schlae/goodgreat-ds3/GreengateDS3.kicad_sch

## KiCad design GreengateDS3.kicad_sch (2024-04-06)

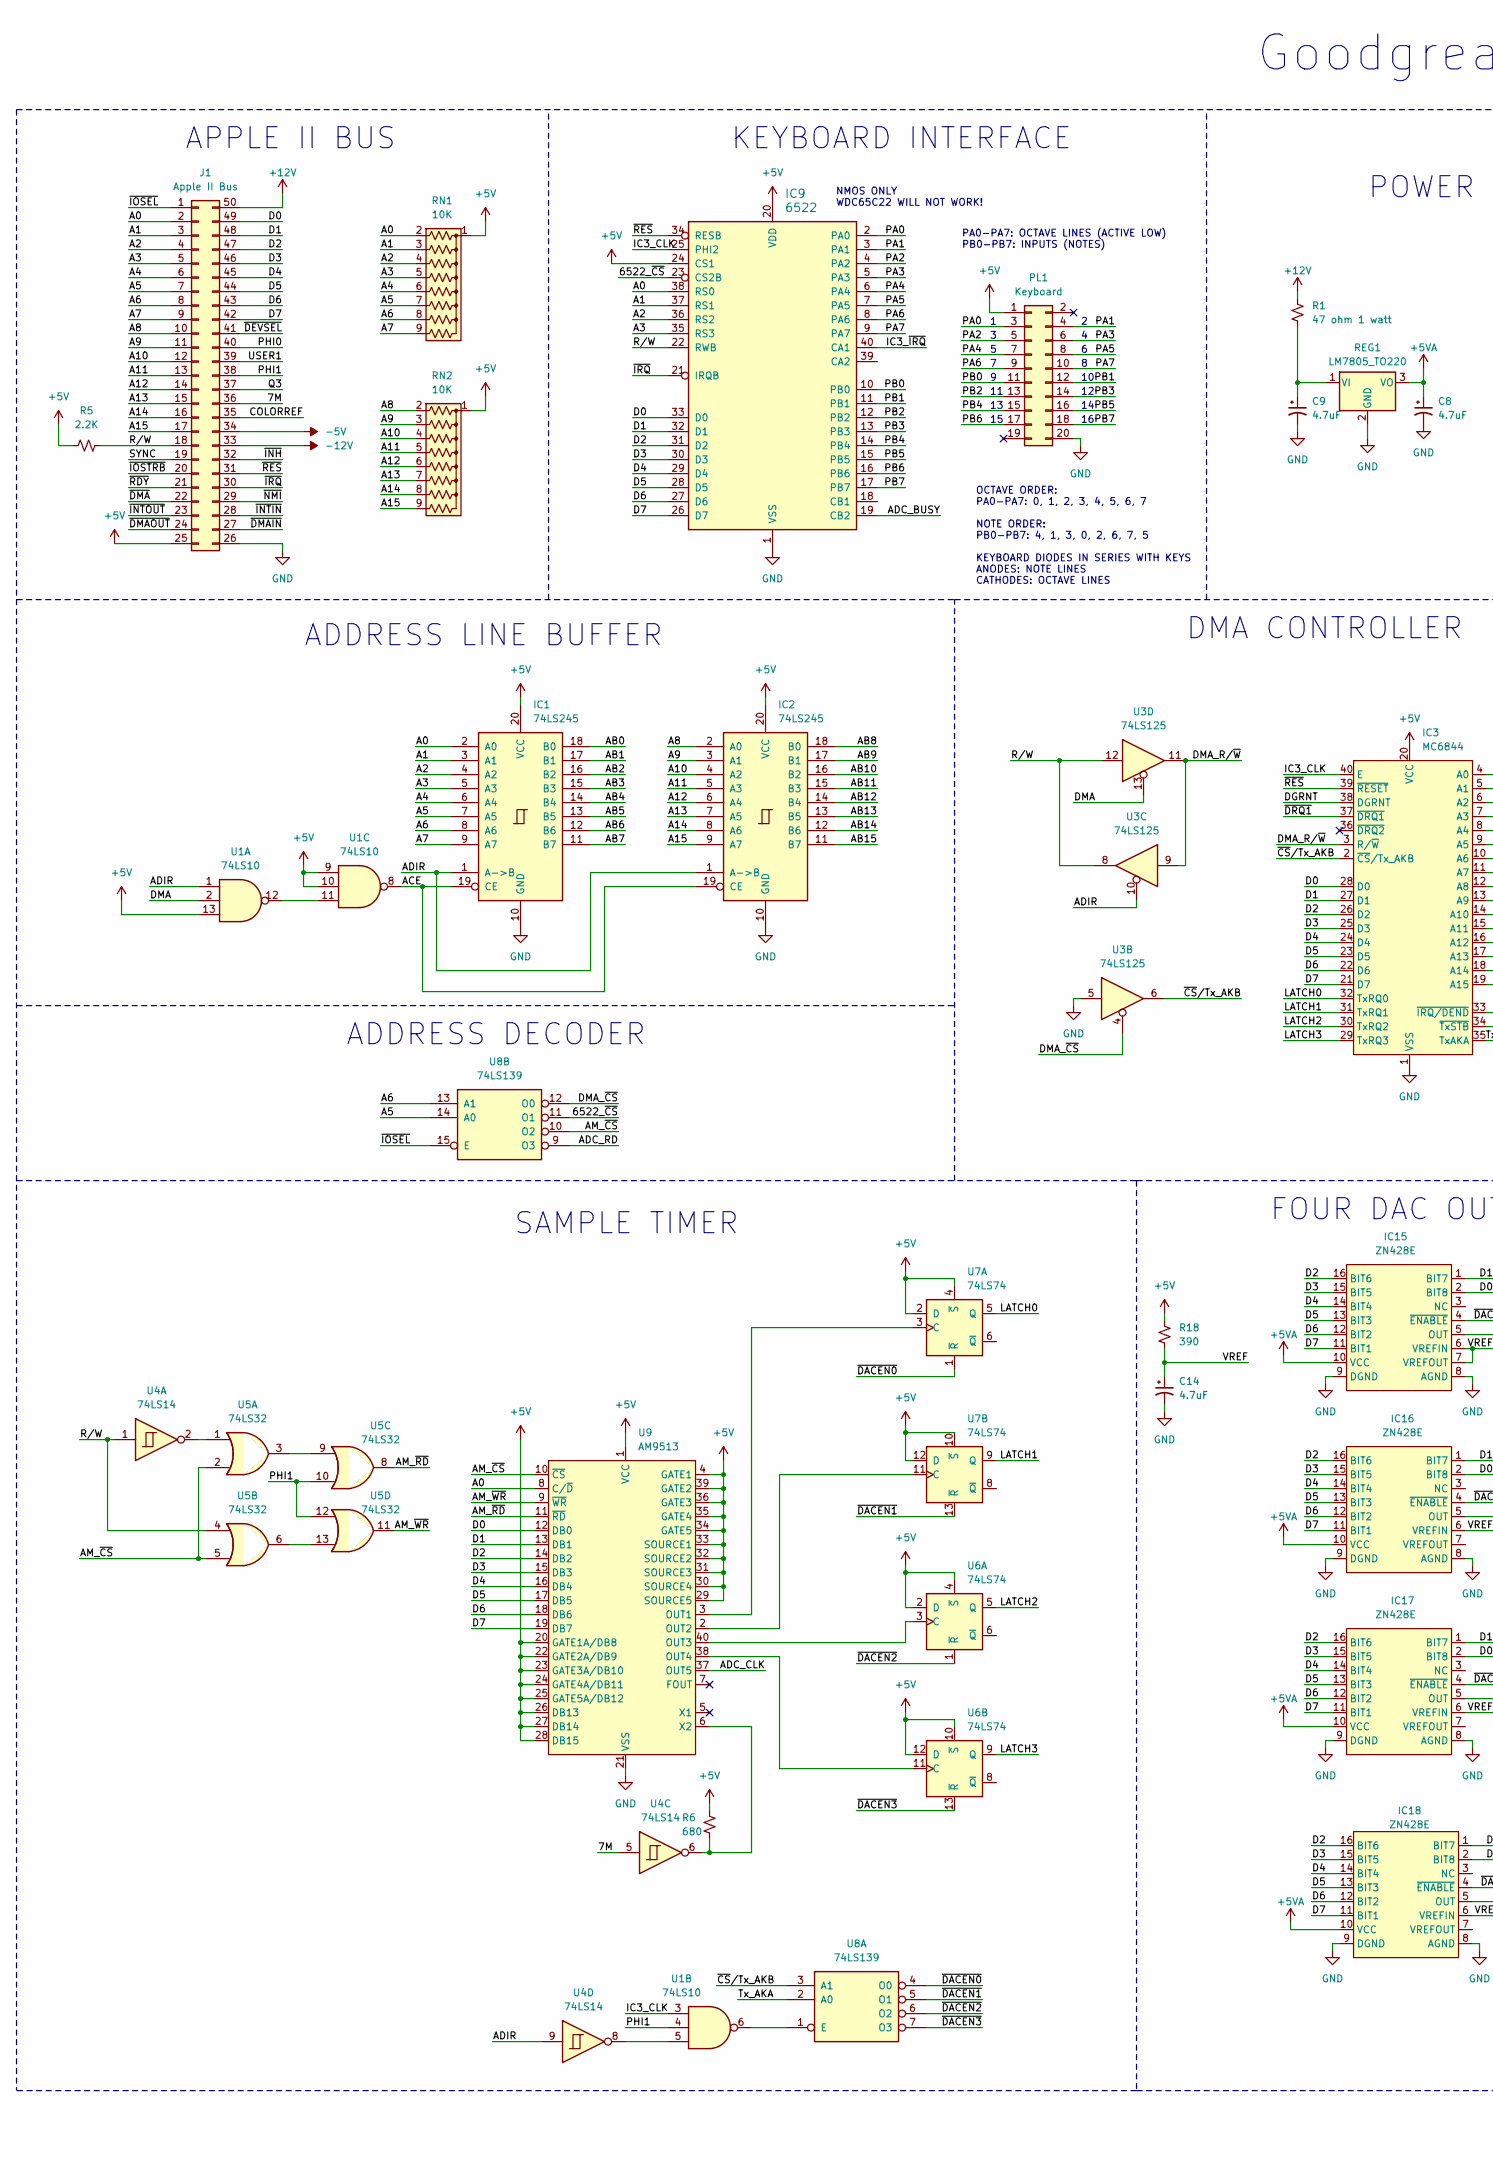
[picture p4: schematic GreengateDS3.kicad_sch, part in row 1, column 1]

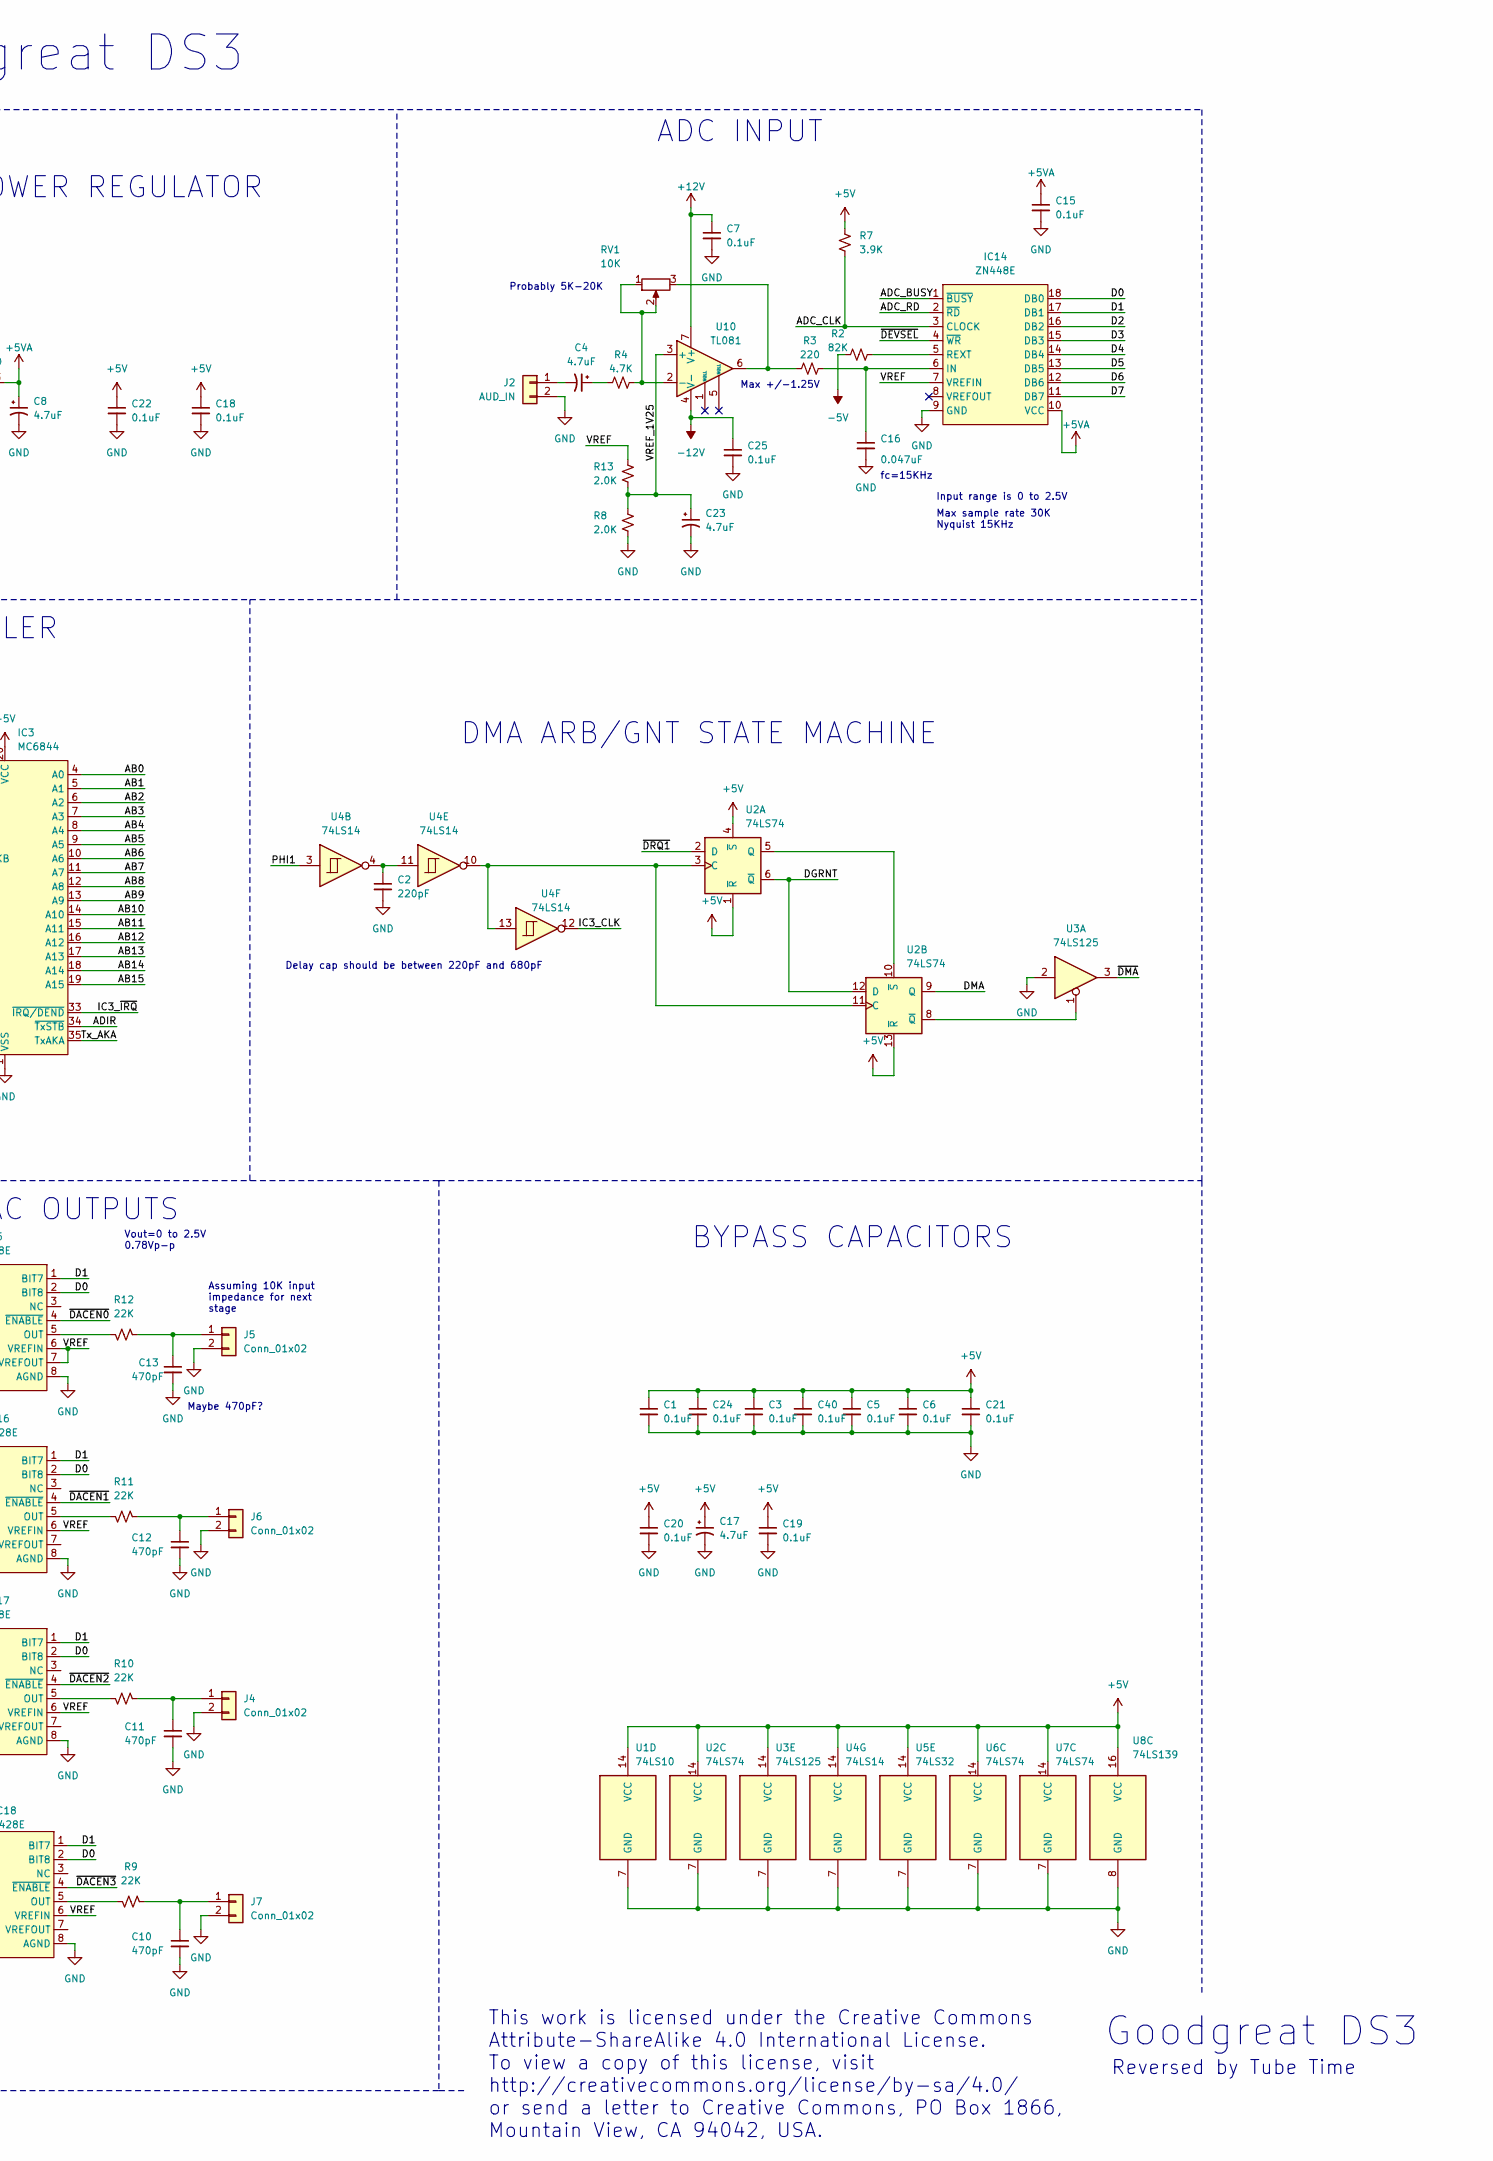
[picture p5: schematic GreengateDS3.kicad_sch, part in row 1, column 2]

Parts:
C1, C3, C5, C6, C7, C15, C18, C19, C20, C21, C22, C24, C25, C40: 0.1uF; CAPAC200
C2: 220pF; CAPAC200
C4, C8, C9, C14, C17, C23: 4.7uF; CAPAP200
C10, C11, C12, C13: 470pF; CAPAC200
C16: 0.047uF; CAPAC200
IC1, IC2: 74LS245; DIP254P762X635-20
IC3: MC6844; DIP254P1524X635-40
IC9: 6522; DIP254P1524X635-40
IC14: ZN448E; DIP254P762X635-18
IC15, IC16, IC17, IC18: ZN428E; DIP254P762X635-16
J1: Apple II Bus; BUS_APPLE2
J2: AUD_IN; SolderWire-0.1sqmm_1x02_P3.6mm_D0.4mm_OD1mm
J4, J7: Conn_01x02; PinHeader_1x02_P2.54mm_Vertical
J5, J6: Conn_01x02; SolderWire-0.1sqmm_1x02_P3.6mm_D0.4mm_OD1mm
PL1: Keyboard; PinHeader_2x10_P2.54mm_Vertical
R1: 47 ohm 1 watt; R_Axial_DIN0309_L9.0mm_D3.2mm_P20.32mm_Horizontal; Mouser 279-CFR100J47R
R2: 82K; R_Axial_DIN0309_L9.0mm_D3.2mm_P12.70mm_Horizontal
R3: 220; R_Axial_DIN0309_L9.0mm_D3.2mm_P12.70mm_Horizontal
R4: 4.7K; R_Axial_DIN0309_L9.0mm_D3.2mm_P12.70mm_Horizontal
R5: 2.2K; R_Axial_DIN0309_L9.0mm_D3.2mm_P12.70mm_Horizontal
R6: 680; R_Axial_DIN0309_L9.0mm_D3.2mm_P12.70mm_Horizontal
R7: 3.9K; R_Axial_DIN0309_L9.0mm_D3.2mm_P12.70mm_Horizontal
R8, R13: 2.0K; R_Axial_DIN0309_L9.0mm_D3.2mm_P12.70mm_Horizontal
R9, R10, R11, R12: 22K; R_Axial_DIN0309_L9.0mm_D3.2mm_P12.70mm_Horizontal
R18: 390; R_Axial_DIN0309_L9.0mm_D3.2mm_P12.70mm_Horizontal
REG1: LM7805_TO220; TO-220-3_Horizontal_TabDown
RN1, RN2: 10K; R_Array_SIP9
RV1: 10K; Potentiometer_Bourns_3339W_Horizontal
U1: 74LS10; DIP254P762X635-14
U2, U6, U7: 74LS74; DIP254P762X635-14
U3: 74LS125; DIP254P762X635-14
U4: 74LS14; DIP254P762X635-14
U5: 74LS32; DIP254P762X635-14
U8: 74LS139; DIP254P762X635-16
U9: AM9513; DIP254P1524X635-40
U10: TL081; DIP254P762X635-8

Connections:
7M: J1.36, U4.5
6522_~CS: IC9.23 (CS2B), U8.11 (O1)
+5V: C1.1, C3.1, C5.1, C6.1, C17.1, C18.1, C19.1, C20.1, C21.1, C22.1, C24.1, C40.1, IC1.20 (VCC), IC2.20 (VCC), IC3.20 (VCC), IC9.20 (VDD), IC9.24 (CS1), J1.25, PL1.1, R5.1, R6.2, R7.2, R18.2, RN1.1 (common), RN2.1 (common), U1.9, U1.10, U1.13, U1.14 (VCC), U2.1 (~R), U2.4 (~S), U2.13 (~R), U2.14 (VCC), U3.14 (VCC), U4.14 (VCC), U5.14 (VCC), U6.2 (D), U6.4 (~S), U6.10 (~S), U6.12 (D), U6.14 (VCC), U7.2 (D), U7.4 (~S), U7.10 (~S), U7.12 (D), U7.14 (VCC), U8.16 (VCC), U9.1 (VCC), U9.4 (GATE1), U9.20 (GATE1A/DB8), U9.22 (GATE2A/DB9), U9.23 (GATE3A/DB10), U9.24 (GATE4A/DB11), U9.25 (GATE5A/DB12), U9.26 (DB13), U9.27 (DB14), U9.28 (DB15), U9.29 (SOURCE5), U9.30 (SOURCE4), U9.31 (SOURCE3), U9.32 (SOURCE2), U9.33 (SOURCE1), U9.34 (GATE5), U9.35 (GATE4), U9.36 (GATE3), U9.39 (GATE2)
+5VA: C8.1, C15.1, IC14.10 (VCC), IC15.10 (VCC), IC16.10 (VCC), IC17.10 (VCC), IC18.10 (VCC), REG1.3 (VO)
+12V: C7.1, J1.50, R1.1, U10.7 (V+)
-5V: J1.34, R2.1
-12V: C25.1, J1.33, U10.4 (V-)
A0: IC1.2 (A0), IC9.38 (RS0), J1.2, RN1.2 (R1), U9.8 (C/~D)
A1: IC1.3 (A1), IC9.37 (RS1), J1.3, RN1.3 (R2)
A2: IC1.4 (A2), IC9.36 (RS2), J1.4, RN1.4 (R3)
A3: IC1.5 (A3), IC9.35 (RS3), J1.5, RN1.5 (R4)
A4: IC1.6 (A4), J1.6, RN1.6 (R5)
A5: IC1.7 (A5), J1.7, RN1.7 (R6), U8.14 (A0)
A6: IC1.8 (A6), J1.8, RN1.8 (R7), U8.13 (A1)
A7: IC1.9 (A7), J1.9, RN1.9 (R8)
A8: IC2.2 (A0), J1.10, RN2.2 (R1)
A9: IC2.3 (A1), J1.11, RN2.3 (R2)
A10: IC2.4 (A2), J1.12, RN2.4 (R3)
A11: IC2.5 (A3), J1.13, RN2.5 (R4)
A12: IC2.6 (A4), J1.14, RN2.6 (R5)
A13: IC2.7 (A5), J1.15, RN2.7 (R6)
A14: IC2.8 (A6), J1.16, RN2.8 (R7)
A15: IC2.9 (A7), J1.17, RN2.9 (R8)
AB0: IC1.18 (B0), IC3.4 (A0)
AB1: IC1.17 (B1), IC3.5 (A1)
AB2: IC1.16 (B2), IC3.6 (A2)
AB3: IC1.15 (B3), IC3.7 (A3)
AB4: IC1.14 (B4), IC3.8 (A4)
AB5: IC1.13 (B5), IC3.9 (A5)
AB6: IC1.12 (B6), IC3.10 (A6)
AB7: IC1.11 (B7), IC3.11 (A7)
AB8: IC2.18 (B0), IC3.12 (A8)
AB9: IC2.17 (B1), IC3.13 (A9)
AB10: IC2.16 (B2), IC3.14 (A10)
AB11: IC2.15 (B3), IC3.15 (A11)
AB12: IC2.14 (B4), IC3.16 (A12)
AB13: IC2.13 (B5), IC3.17 (A13)
AB14: IC2.12 (B6), IC3.18 (A14)
AB15: IC2.11 (B7), IC3.19 (A15)
ACE: IC1.19 (CE), IC2.19 (CE), U1.8
ADC_BUSY: IC9.19 (CB2), IC14.1 (~BUSY)
ADC_CLK: IC14.3 (CLOCK), R7.1, U9.37 (OUT5)
ADC_RD: IC14.2 (~RD), U8.9 (O3)
ADIR: IC1.1 (A->B), IC2.1 (A->B), IC3.34 (~TxSTB), U1.1, U3.10, U4.9
AM_~CS: U5.2, U5.5, U8.10 (O2), U9.10 (~CS)
AM_~RD: U5.8, U9.11 (~RD)
AM_~WR: U5.11, U9.9 (~WR)
COLORREF: J1.35
D0: IC3.28 (D0), IC9.33 (D0), IC14.18 (DB0), IC15.2 (BIT8), IC16.2 (BIT8), IC17.2 (BIT8), IC18.2 (BIT8), J1.49, U9.12 (DB0)
D1: IC3.27 (D1), IC9.32 (D1), IC14.17 (DB1), IC15.1 (BIT7), IC16.1 (BIT7), IC17.1 (BIT7), IC18.1 (BIT7), J1.48, U9.13 (DB1)
D2: IC3.26 (D2), IC9.31 (D2), IC14.16 (DB2), IC15.16 (BIT6), IC16.16 (BIT6), IC17.16 (BIT6), IC18.16 (BIT6), J1.47, U9.14 (DB2)
D3: IC3.25 (D3), IC9.30 (D3), IC14.15 (DB3), IC15.15 (BIT5), IC16.15 (BIT5), IC17.15 (BIT5), IC18.15 (BIT5), J1.46, U9.15 (DB3)
D4: IC3.24 (D4), IC9.29 (D4), IC14.14 (DB4), IC15.14 (BIT4), IC16.14 (BIT4), IC17.14 (BIT4), IC18.14 (BIT4), J1.45, U9.16 (DB4)
D5: IC3.23 (D5), IC9.28 (D5), IC14.13 (DB5), IC15.13 (BIT3), IC16.13 (BIT3), IC17.13 (BIT3), IC18.13 (BIT3), J1.44, U9.17 (DB5)
D6: IC3.22 (D6), IC9.27 (D6), IC14.12 (DB6), IC15.12 (BIT2), IC16.12 (BIT2), IC17.12 (BIT2), IC18.12 (BIT2), J1.43, U9.18 (DB6)
D7: IC3.21 (D7), IC9.26 (D7), IC14.11 (DB7), IC15.11 (BIT1), IC16.11 (BIT1), IC17.11 (BIT1), IC18.11 (BIT1), J1.42, U9.19 (DB7)
DGRNT: IC3.38 (DGRNT), U2.6 (~Q), U2.12 (D)
DMA: U1.2, U2.9 (Q), U3.13
DMA_R/~W: IC3.3 (R/~W), U3.9, U3.11
DMA_~CS: U3.4, U8.12 (O0)
GND: C1.2, C2.2, C3.2, C5.2, C6.2, C7.2, C8.2, C9.2, C10.2, C11.2, C12.2, C13.2, C14.2, C15.2, C16.2, C17.2, C18.2, C19.2, C20.2, C21.2, C22.2, C23.2, C24.2, C25.2, C40.2, IC1.10 (GND), IC2.10 (GND), IC3.1 (VSS), IC9.1 (VSS), IC14.9 (GND), IC15.8 (AGND), IC15.9 (DGND), IC16.8 (AGND), IC16.9 (DGND), IC17.8 (AGND), IC17.9 (DGND), IC18.8 (AGND), IC18.9 (DGND), J1.26, J2.2, J4.2, J5.2, J6.2, J7.2, PL1.20, R8.1, REG1.2 (GND), U1.7 (GND), U2.7 (GND), U3.2, U3.5, U3.7 (GND), U4.7 (GND), U5.7 (GND), U6.7 (GND), U7.7 (GND), U8.8 (GND), U9.21 (VSS)
IC3_CLK: IC3.40 (E), IC9.25 (PHI2), U1.3, U4.12
IC3_~IRQ: IC3.33 (~IRQ/DEND), IC9.40 (CA1)
LATCH0: IC3.32 (TxRQ0), U7.5 (Q)
LATCH1: IC3.31 (TxRQ1), U7.9 (Q)
LATCH2: IC3.30 (TxRQ2), U6.5 (Q)
LATCH3: IC3.29 (TxRQ3), U6.9 (Q)
unnamed: C2.1, U4.4, U4.11
unnamed: C4.1, R4.1
unnamed: C4.2, J2.1
unnamed: C9.1, R1.2, REG1.1 (VI)
unnamed: C10.1, J7.1, R9.1
unnamed: C11.1, J4.1, R10.1
unnamed: C12.1, J6.1, R11.1
unnamed: C13.1, J5.1, R12.1
unnamed: C16.1, IC14.6 (IN), R3.2
unnamed: IC14.5 (REXT), R2.2
unnamed: IC15.5 (OUT), R12.2
unnamed: IC16.5 (OUT), R11.2
unnamed: IC17.5 (OUT), R10.2
unnamed: IC18.5 (OUT), R9.2
unnamed: R3.1, RV1.3, U10.6
unnamed: R4.2, RV1.1, RV1.2, U10.2 (-)
unnamed: R6.1, U4.6, U9.6 (X2)
unnamed: U1.5, U4.8
unnamed: U1.6, U8.1 (E)
unnamed: U1.11, U1.12
unnamed: U2.8 (~Q), U3.1
unnamed: U2.5 (Q), U2.10 (~S)
unnamed: U2.3 (C), U2.11 (C), U4.10, U4.13
unnamed: U4.2, U5.1
unnamed: U5.3, U5.9
unnamed: U5.6, U5.13
unnamed: U6.3 (C), U9.40 (OUT3)
unnamed: U6.11 (C), U9.38 (OUT4)
unnamed: U7.3 (C), U9.3 (OUT1)
unnamed: U7.11 (C), U9.2 (OUT2)
PA0: IC9.2 (PA0), PL1.3
PA1: IC9.3 (PA1), PL1.4
PA2: IC9.4 (PA2), PL1.5
PA3: IC9.5 (PA3), PL1.6
PA4: IC9.6 (PA4), PL1.7
PA5: IC9.7 (PA5), PL1.8
PA6: IC9.8 (PA6), PL1.9
PA7: IC9.9 (PA7), PL1.10
PB0: IC9.10 (PB0), PL1.11
PB1: IC9.11 (PB1), PL1.12
PB2: IC9.12 (PB2), PL1.13
PB3: IC9.13 (PB3), PL1.14
PB4: IC9.14 (PB4), PL1.15
PB5: IC9.15 (PB5), PL1.16
PB6: IC9.16 (PB6), PL1.17
PB7: IC9.17 (PB7), PL1.18
PHI0: J1.40
PHI1: J1.38, U1.4, U4.3, U5.10, U5.12
Q3: J1.37
R/W: IC9.22 (RWB), J1.18, R5.2, U3.8, U3.12, U4.1, U5.4
SYNC: J1.19
Tx_AKA: IC3.35 (TxAKA), U8.2 (A0)
USER1: J1.39
VREF: C14.1, IC14.7 (VREFIN), IC15.6 (VREFIN), IC15.7 (VREFOUT), IC16.6 (VREFIN), IC17.6 (VREFIN), IC18.6 (VREFIN), R13.1, R18.1
VREF_1V25: C23.1, R8.2, R13.2, U10.3 (+)
~CS/Tx_AKB: IC3.2 (~CS/Tx_AKB), U3.6, U8.3 (A1)
~DACEN0: IC15.4 (~ENABLE), U7.1 (~R), U8.4 (O0)
~DACEN1: IC16.4 (~ENABLE), U7.13 (~R), U8.5 (O1)
~DACEN2: IC17.4 (~ENABLE), U6.1 (~R), U8.6 (O2)
~DACEN3: IC18.4 (~ENABLE), U6.13 (~R), U8.7 (O3)
~DEVSEL: IC14.4 (~WR), J1.41
~DMAIN: J1.27
~DMAOUT: J1.24
~DMA: J1.22, U3.3
~DRQ1: IC3.37 (~DRQ1), U2.2 (D)
~INH: J1.32
~INTIN: J1.28
~INTOUT: J1.23
~IOSEL: J1.1, U8.15 (E)
~IOSTRB: J1.20
~IRQ: IC9.21 (IRQB), J1.30
~NMI: J1.29
~RDY: J1.21
~RES: IC3.39 (~RESET), IC9.34 (RESB), J1.31

Notes on the sheet:
Probably 5K-20K
Delay cap should be between 220pF and 680pF
DMA CONTROLLER
Vout=0 to 2.5V 0.78Vp-p
SAMPLE TIMER
Goodgreat DS3
Maybe 470pF?
PA0-PA7: OCTAVE LINES (ACTIVE LOW) PB0-PB7: INPUTS (NOTES)
This work is licensed under the Creative Commons Attribute-ShareAlike 4.0 International License. To view a copy of this license, visit http://creativecommons.org/license/by-sa/4.0/ or send a letter to Creative Commons, PO Box 1866, Mountain View, CA 94042, USA.
Assuming 10K input impedance for next stage
Reversed by Tube Time
DMA ARB/GNT STATE MACHINE
Max +/-1.25V
OCTAVE ORDER: PA0-PA7: 0, 1, 2, 3, 4, 5, 6, 7 NOTE ORDER: PB0-PB7: 4, 1, 3, 0, 2, 6, 7, 5 KEYBOARD DIODES IN SERIES WITH KEYS ANODES: NOTE LINES CATHODES: OCTAVE LINES
ADDRESS DECODER
KEYBOARD INTERFACE
FOUR DAC OUTPUTS
BYPASS CAPACITORS
POWER REGULATOR
APPLE II BUS
ADC INPUT
ADDRESS LINE BUFFER
Input range is 0 to 2.5V
fc=15KHz
NMOS ONLY WDC65C22 WILL NOT WORK!
Max sample rate 30K Nyquist 15KHz
